EliMattingly22/TPA3255_ClassD_PBTL/OutputFilt.asc

C1: cap; 1µ
C2: cap; 10n
C3: cap; 470n
C4: cap; 1n
L1: ind; 10µ; Rser=50m
L2: ind; 20µ; Rser=50m
R1: res; 3.3
R2: res; 50m
R3: res; 4
V1: voltage; ""; AC 40
Named nets: 0
.ac oct 1k 1k 1meg
