EliMattingly22/TPA3255_ClassD_PBTL/StartupCirc.asc

C1: cap; 47u
D1: zener; BZX84C12L
M1: nmos; BSP89
M2: nmos; BSP89
R1: res; 47k
R2: res; 10k
R3: res; 10k
V1: voltage; 12
Named nets: 0
.tran 1 startup
